Lingualizer/MySmartGlen/Display/Platine/Platine Display ESP32-32E .jpeg

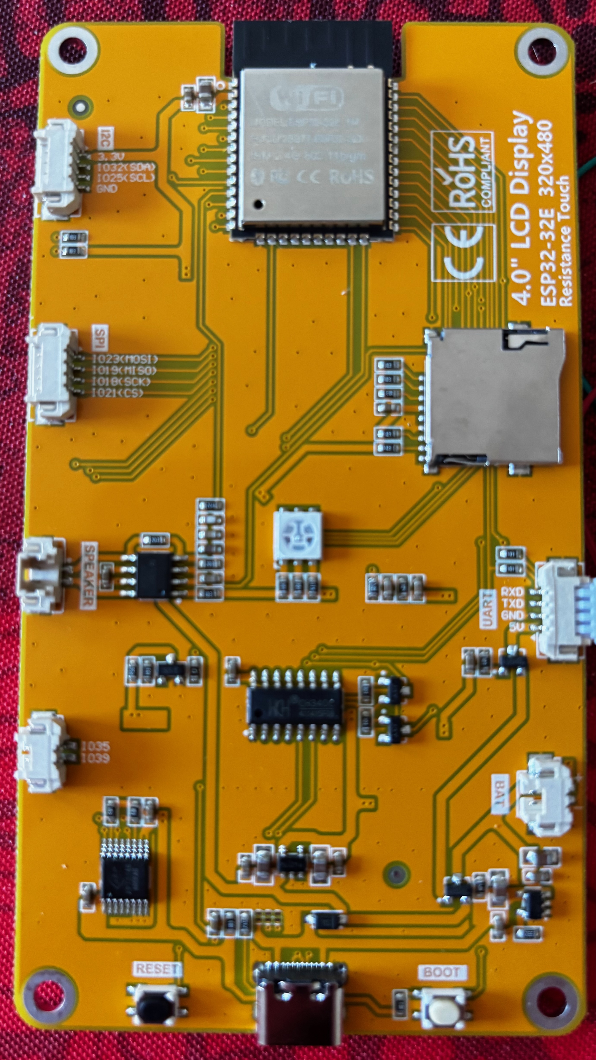
Display/Platine/Platine Display ESP32-32E .jpeg
