Lingualizer/MySmartGlen/Display/Platine/SHT31.jpeg

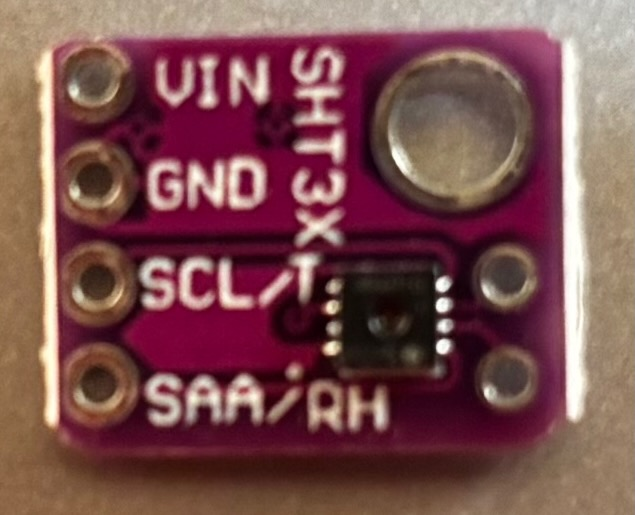
Display/Platine/SHT31.jpeg
