Lingualizer/MySmartGlen/Frischwasser/Platine/ESP32-NodeMCU.jpeg

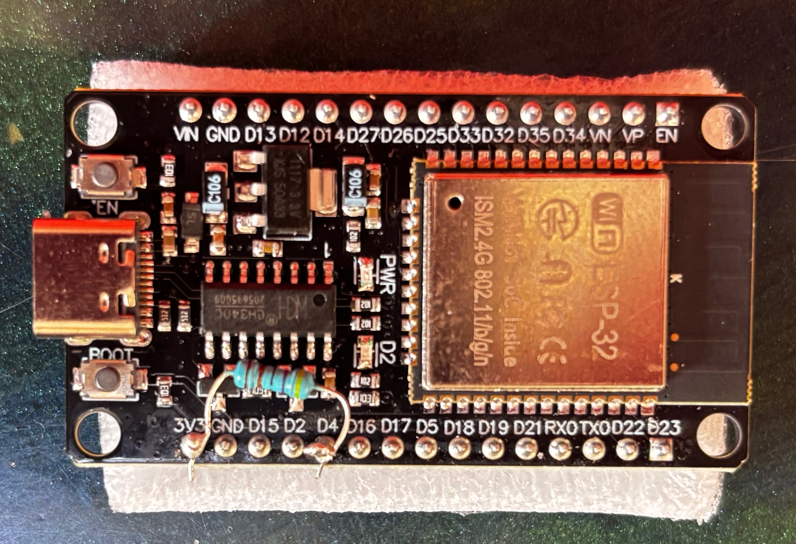
Frischwasser/Platine/ESP32-NodeMCU.jpeg
