Lingualizer/MySmartGlen/Frischwasser/Platine/XKC-Y25-V.png

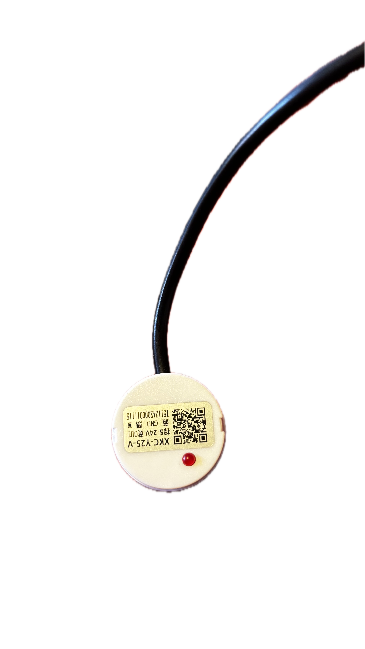
Frischwasser/Platine/XKC-Y25-V.png
