Lingualizer/MySmartGlen/PipiTank/ESP32-NodeMCU.jpeg

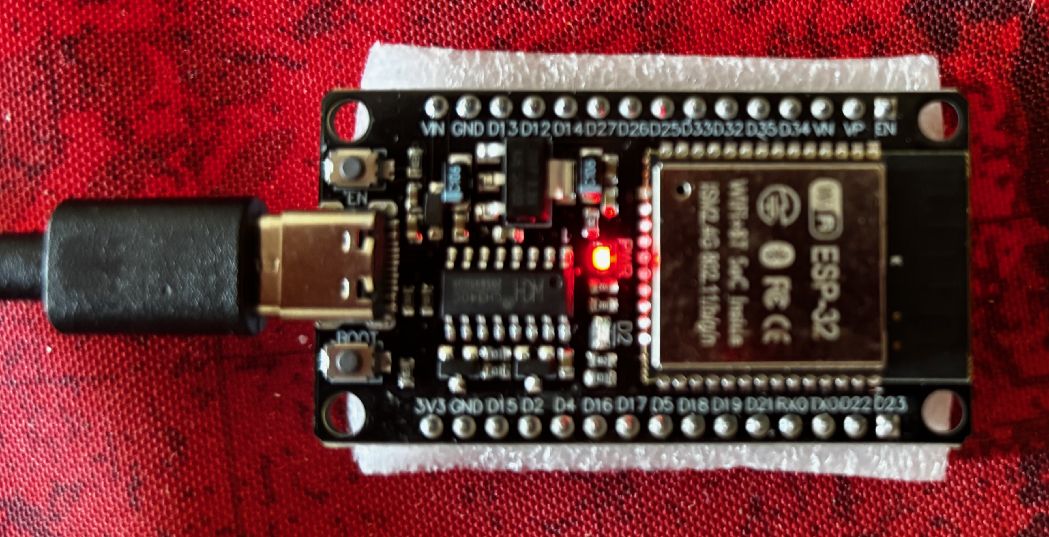
PipiTank/ESP32-NodeMCU.jpeg
