Lingualizer/MySmartGlen/PipiTank/XKC-Y25-NPN.jpeg

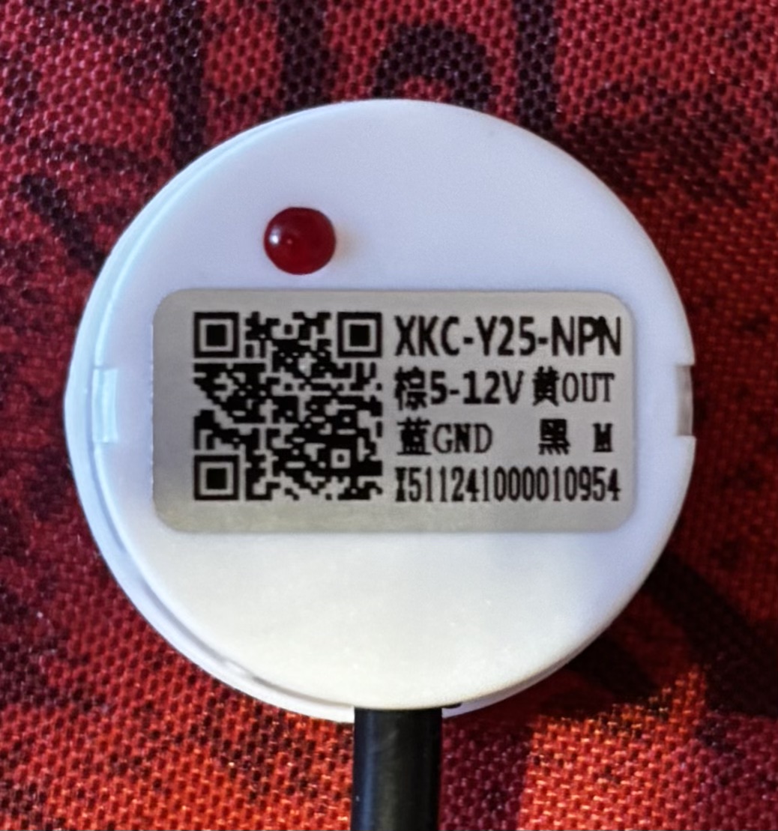
PipiTank/XKC-Y25-NPN.jpeg
