Lingualizer/MySmartGlen/VE.Direkt Solar/VE.Direct - ESP32-Display.png

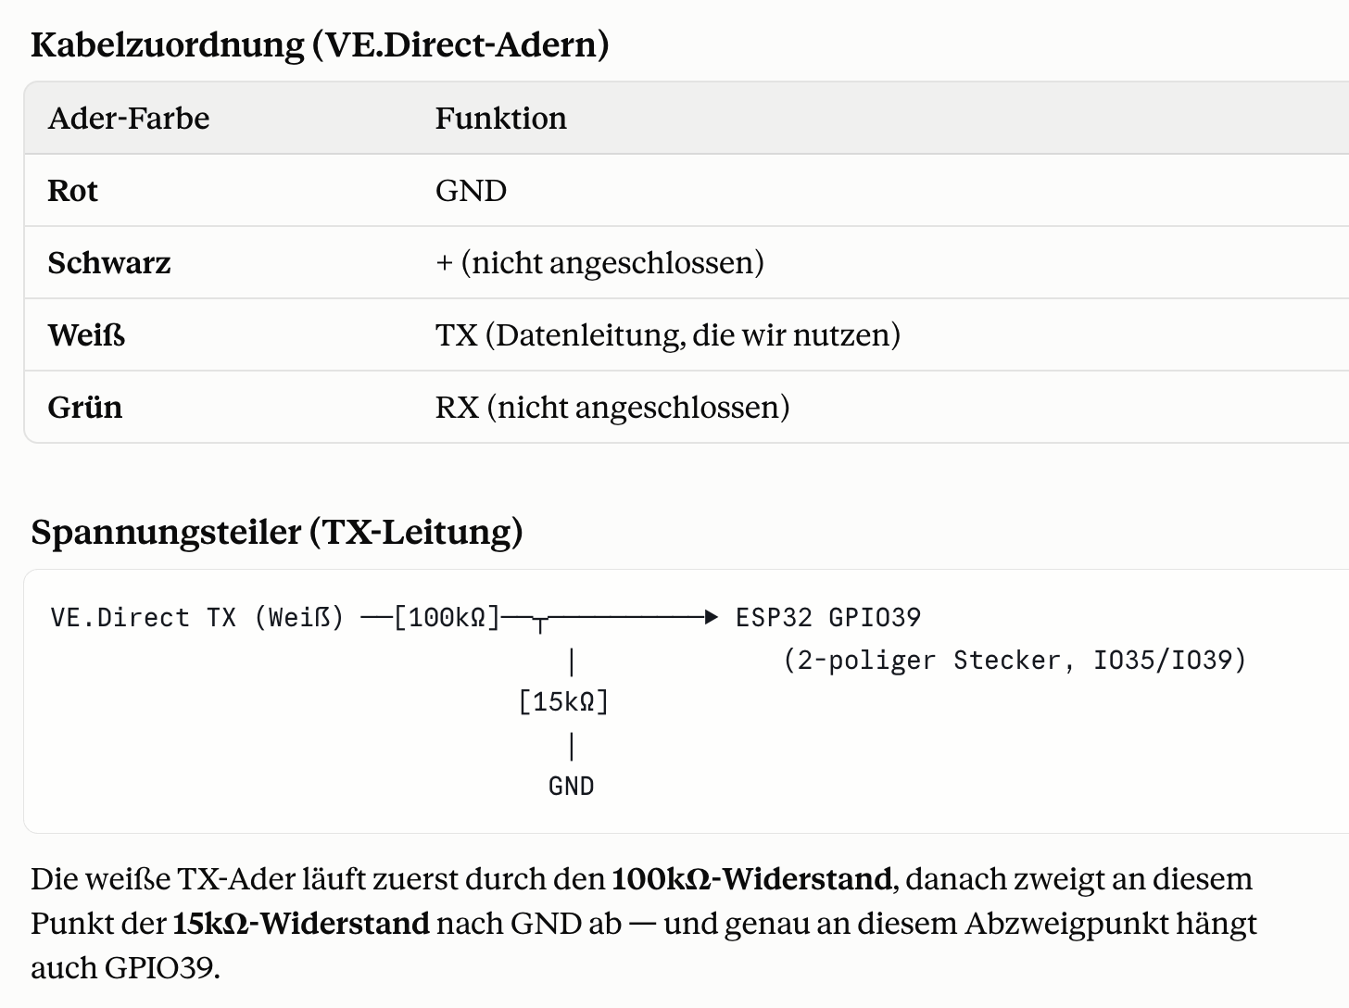
VE.Direkt Solar/VE.Direct - ESP32-Display.png
