Lingualizer/MySmartGlen/VE.Direkt Solar/Victron VE.Direct.jpg

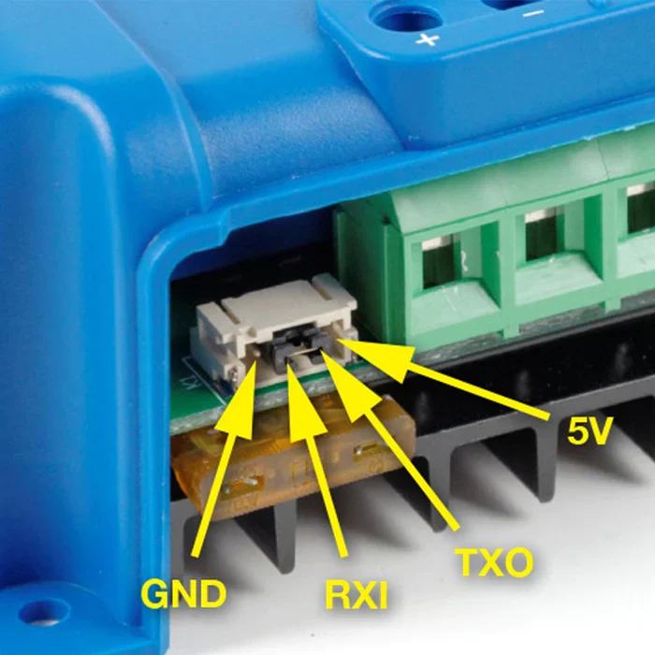
VE.Direkt Solar/Victron VE.Direct.jpg
