Lingualizer/MySmartGlen/Components/BC337 Transistor/BC337 Pins.png

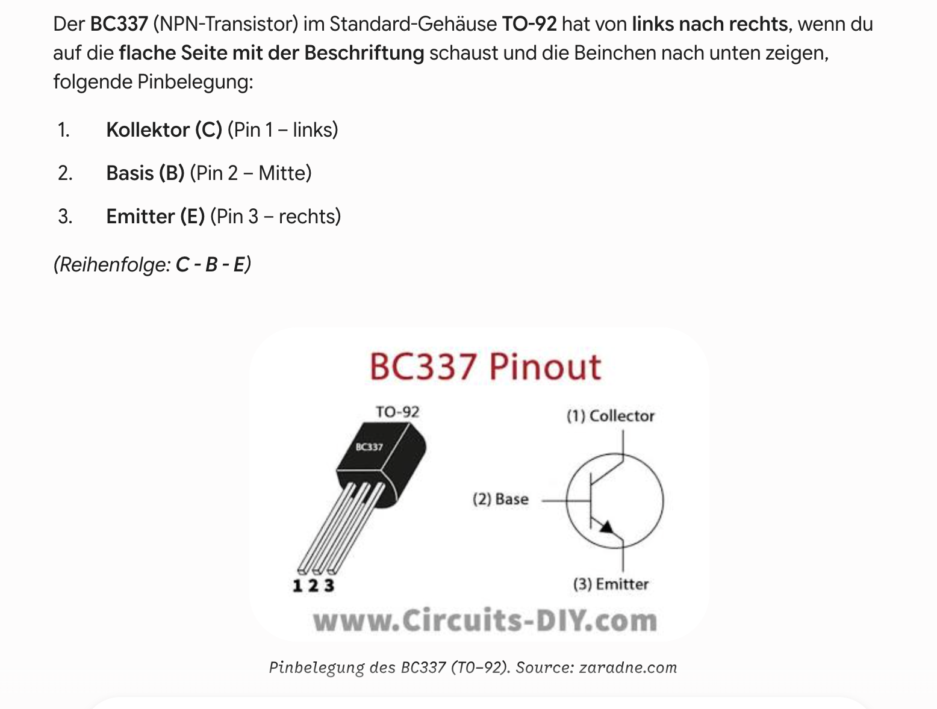
Components/BC337 Transistor/BC337 Pins.png
