Lingualizer/MySmartGlen/Components/VE.Direct Kabel/VE.Direct Kabel.jpg

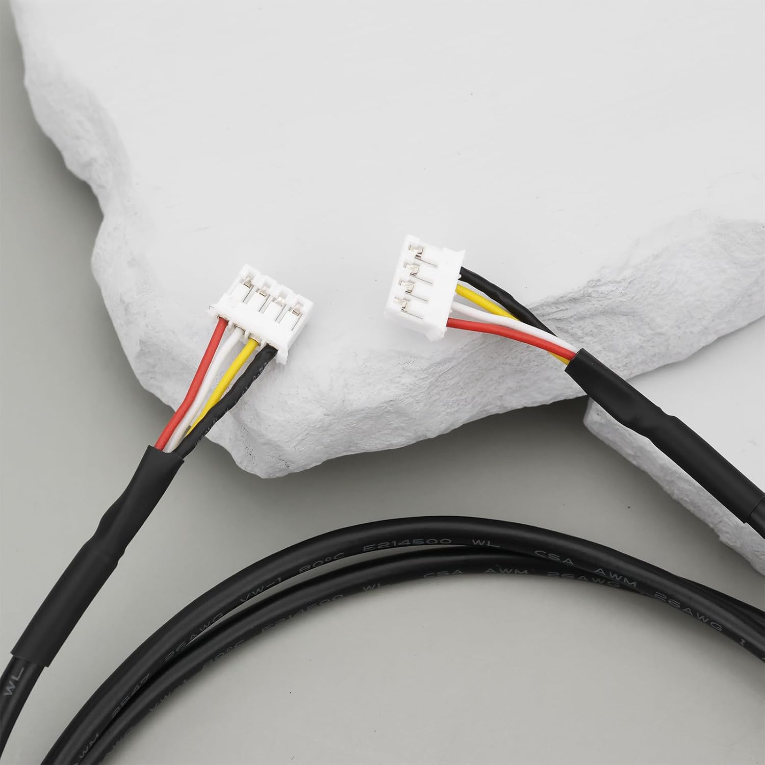
Components/VE.Direct Kabel/VE.Direct Kabel.jpg
