Lingualizer/MySmartGlen/Components/VE.Direct Shunt/VE.Direct Shunt.jpg

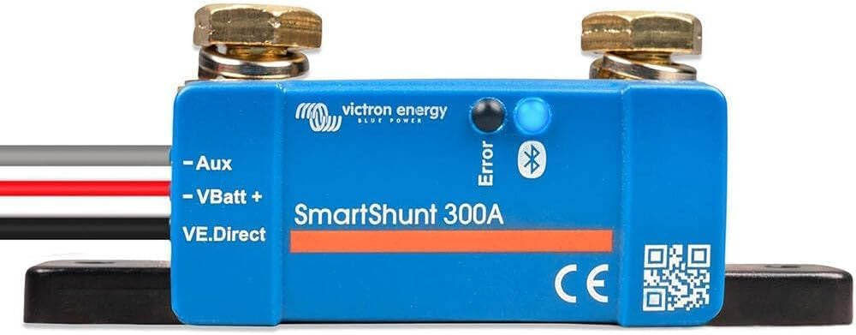
Components/VE.Direct Shunt/VE.Direct Shunt.jpg
