Lingualizer/MySmartGlen/Components/XKC-Y25-NPN/2-XKC-Y25-CN4-Pin-Data.webp

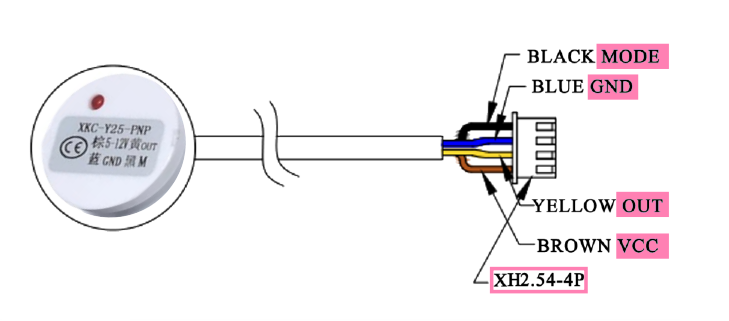
Components/XKC-Y25-NPN/2-XKC-Y25-CN4-Pin-Data.webp
