Lingualizer/MySmartGlen/Components/XKC-Y25-NPN/Wiring XKC-Y25-NPN.jpeg

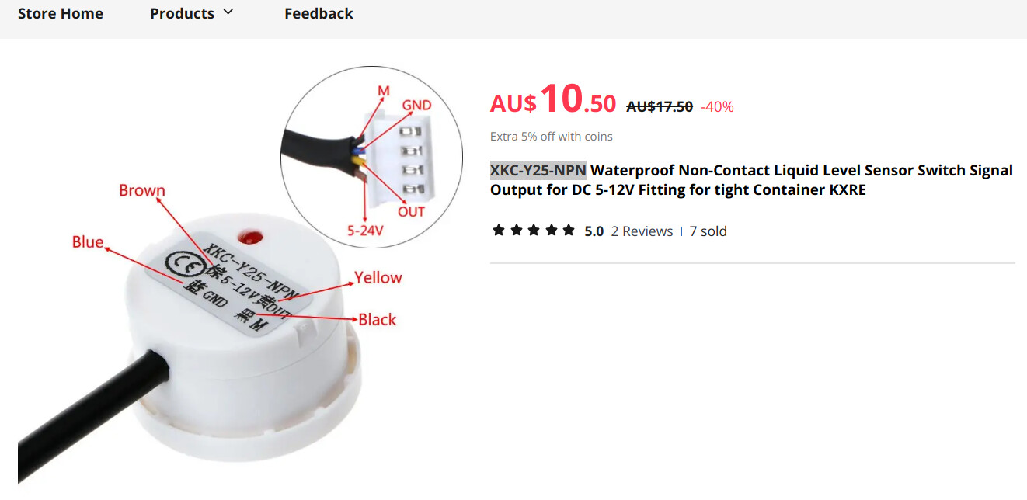
Components/XKC-Y25-NPN/Wiring XKC-Y25-NPN.jpeg
